Francois25/liquid_level_sensor/Docs/pictures/IMG_4032.jpg

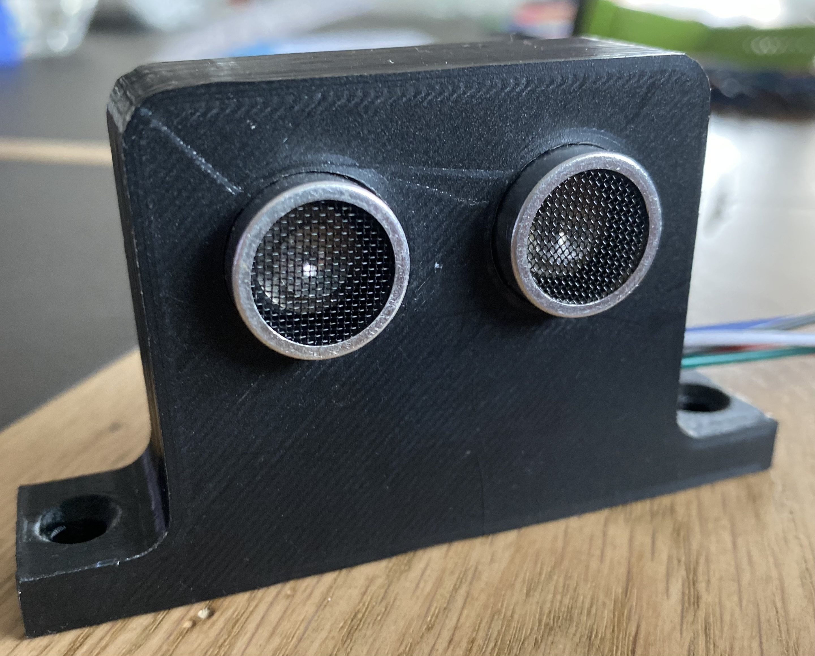
Docs/pictures/IMG_4032.jpg
