Francois25/liquid_level_sensor/Docs/pictures/IMG_4033.jpg

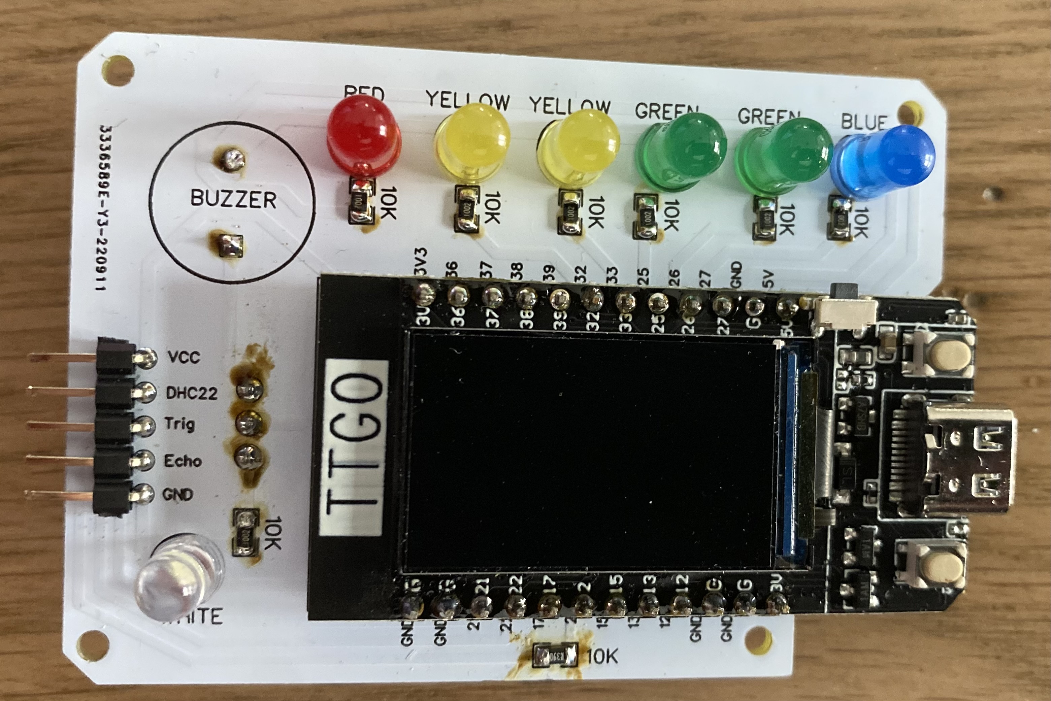
Docs/pictures/IMG_4033.jpg
