Francois25/liquid_level_sensor/Docs/pictures/IMG_4035.jpg

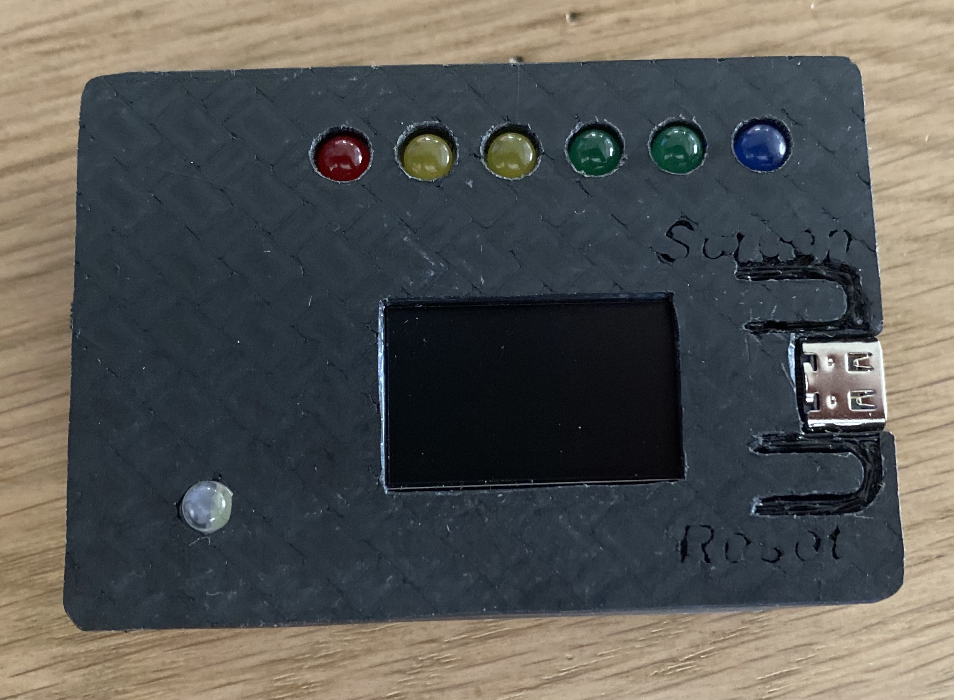
Docs/pictures/IMG_4035.jpg
